HackHype/T2601_APIArduino/T2601_APIArduinoExtentionBoard/M2601_APIArduinoExtentionBoard_Lib3D/CAP-SMD_L4.3-W4.3-H5.3-LS5.1.step

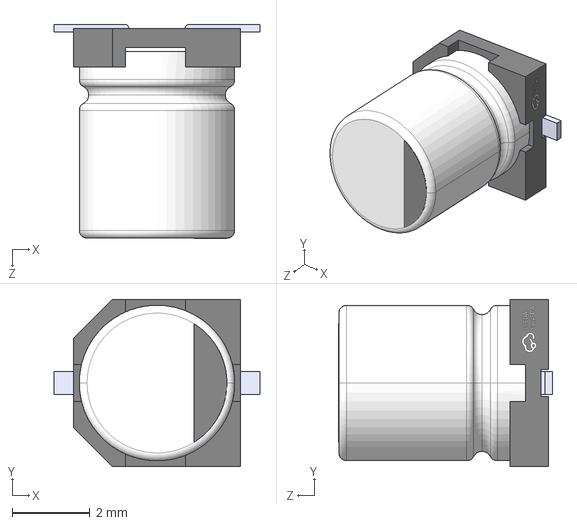
[picture p18: CAD file, 2026-03-15]
T2601_APIArduinoExtentionBoard/M2601_APIArduinoExtentionBoard_Lib3D/CAP-SMD_L4.3-W4.3-H5.3-LS5.1.step
5.30 x 4.30 x 5.51 mm
