HackHype/T2601_APIArduino/T2601_APIArduinoExtentionBoard/M2601_APIArduinoExtentionBoard_Lib3D/USB-C-SMD_HC-TYPE-C-16P-01A.step

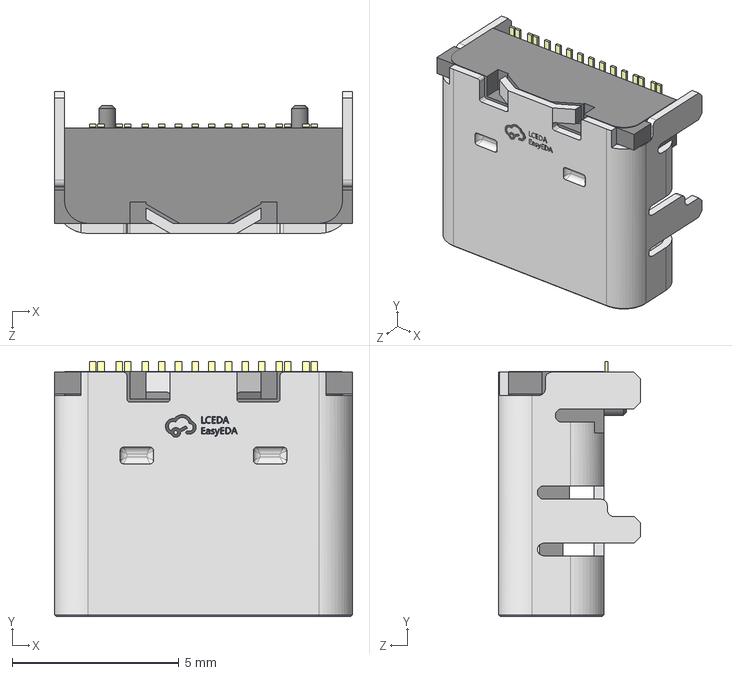
[picture p19: CAD file, 2026-03-15]
T2601_APIArduinoExtentionBoard/M2601_APIArduinoExtentionBoard_Lib3D/USB-C-SMD_HC-TYPE-C-16P-01A.step
8.94 x 7.65 x 4.27 mm
