HackHype/T2601_APIArduino/T2601_APIArduinoExtentionBoard/M2601_APIArduinoExtentionBoard_Lib3D/HTSSOP-16_L5.0-W4.4-P0.65-LS6.4-BL-EP2.5.step

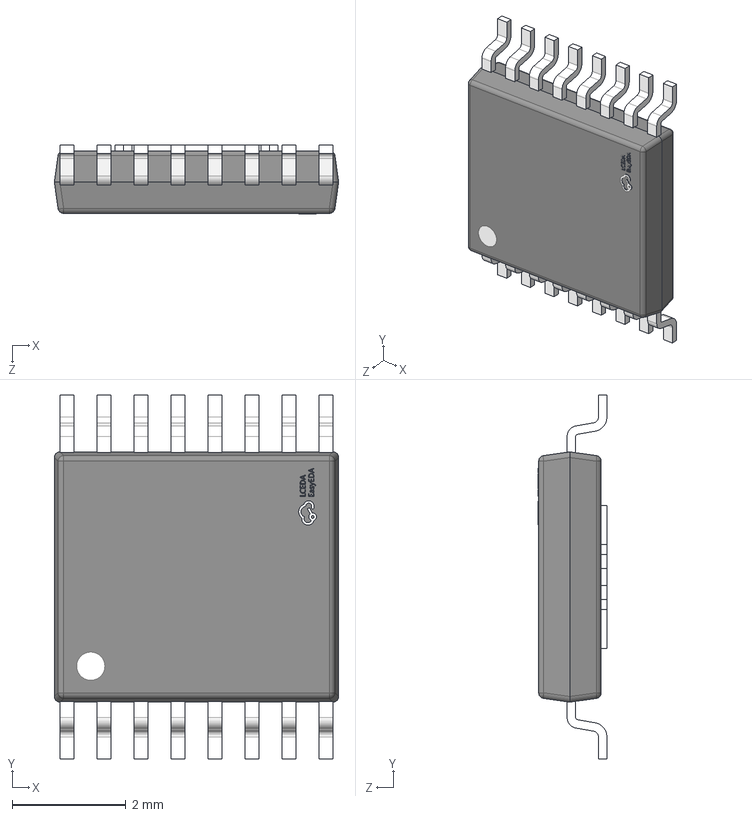
[picture p20: CAD file, 2026-03-15]
T2601_APIArduinoExtentionBoard/M2601_APIArduinoExtentionBoard_Lib3D/HTSSOP-16_L5.0-W4.4-P0.65-LS6.4-BL-EP2.5.step
5.00 x 6.40 x 1.21 mm
