HackHype/T2601_APIArduino/T2601_APIArduinoExtentionBoard/M2601_APIArduinoExtentionBoard_Lib3D/HTSSOP-20_L6.5-W4.4-P0.65-LS6.4-BL-EP3.0.step

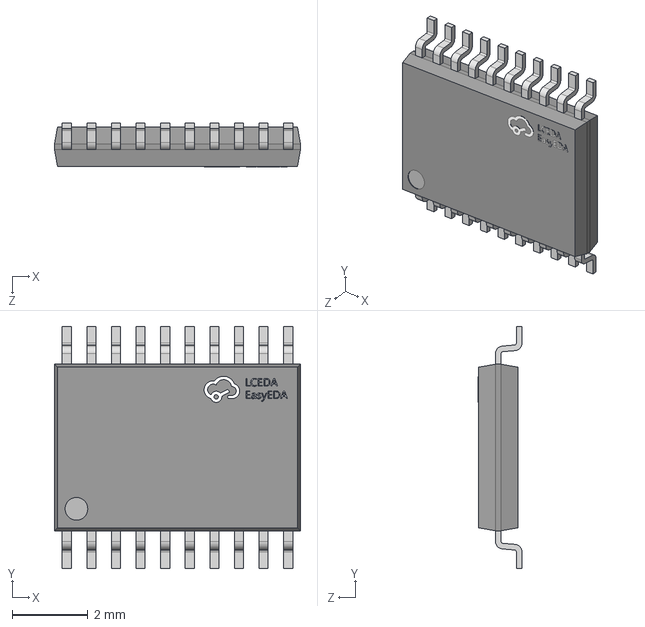
[picture p21: CAD file, 2026-03-15]
T2601_APIArduinoExtentionBoard/M2601_APIArduinoExtentionBoard_Lib3D/HTSSOP-20_L6.5-W4.4-P0.65-LS6.4-BL-EP3.0.step
6.50 x 6.40 x 1.16 mm
