HackHype/T2601_APIArduino/T2601_APIArduinoExtentionBoard/M2601_APIArduinoExtentionBoard_Lib3D/CAP-SMD_BD6.3-L6.6-W6.6-H7.7.step

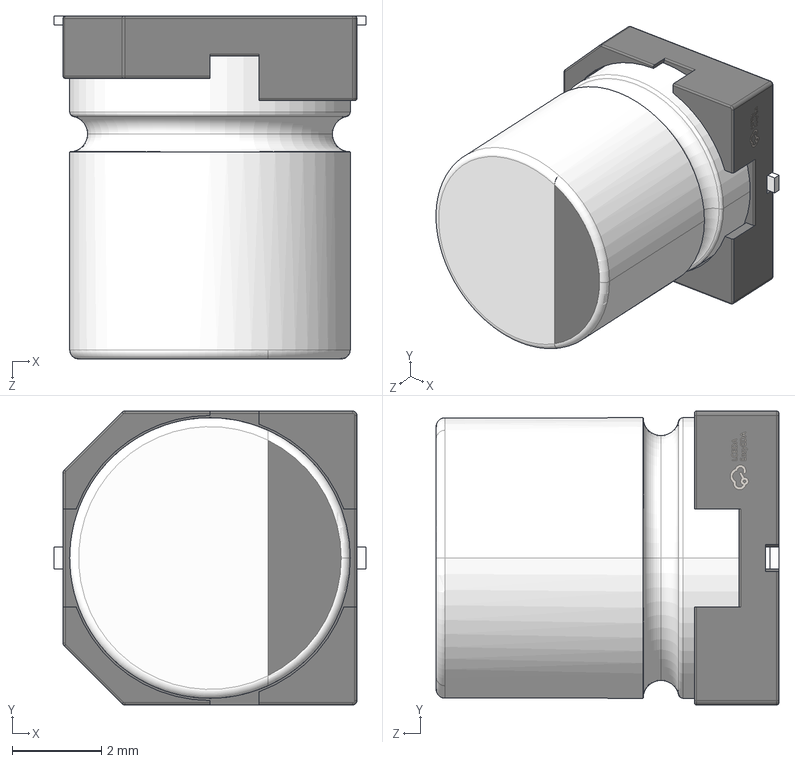
[picture p22: CAD file, 2026-03-15]
T2601_APIArduinoExtentionBoard/M2601_APIArduinoExtentionBoard_Lib3D/CAP-SMD_BD6.3-L6.6-W6.6-H7.7.step
7.00 x 6.60 x 7.70 mm
