HackHype/T2601_APIArduino/T2601_APIArduinoExtentionBoard/M2601_APIArduinoExtentionBoard_Lib3D/QFN-16_L3.0-W3.0-H0.9-P0.50.step

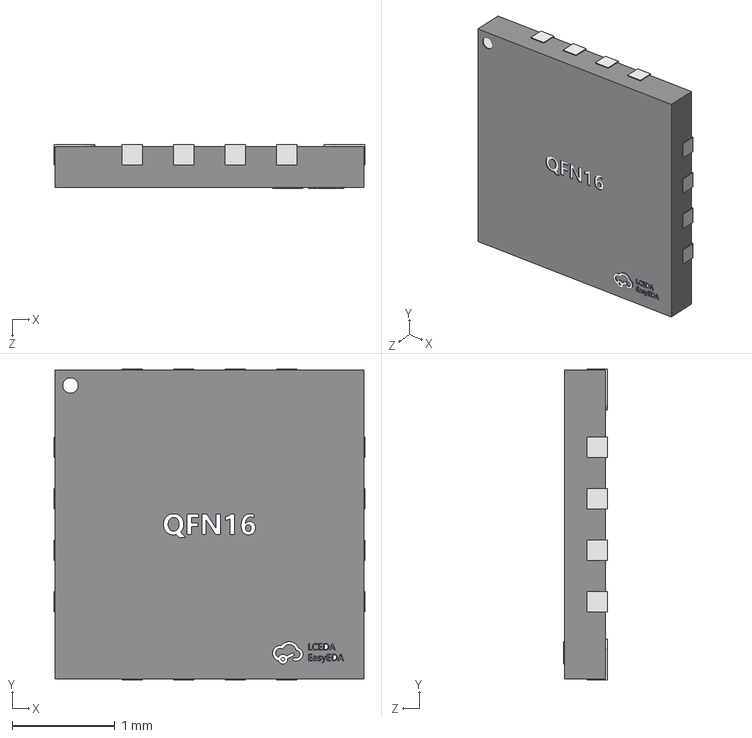
[picture p23: CAD file, 2026-03-15]
T2601_APIArduinoExtentionBoard/M2601_APIArduinoExtentionBoard_Lib3D/QFN-16_L3.0-W3.0-H0.9-P0.50.step
3.02 x 3.02 x 0.43 mm
