HackHype/T2601_APIArduino/T2601_APIArduinoExtentionBoard/M2601_APIArduinoExtentionBoard_Lib3D/IND-SMD_L5.0-W5.0-LQH5BPN1R5NT0L.step

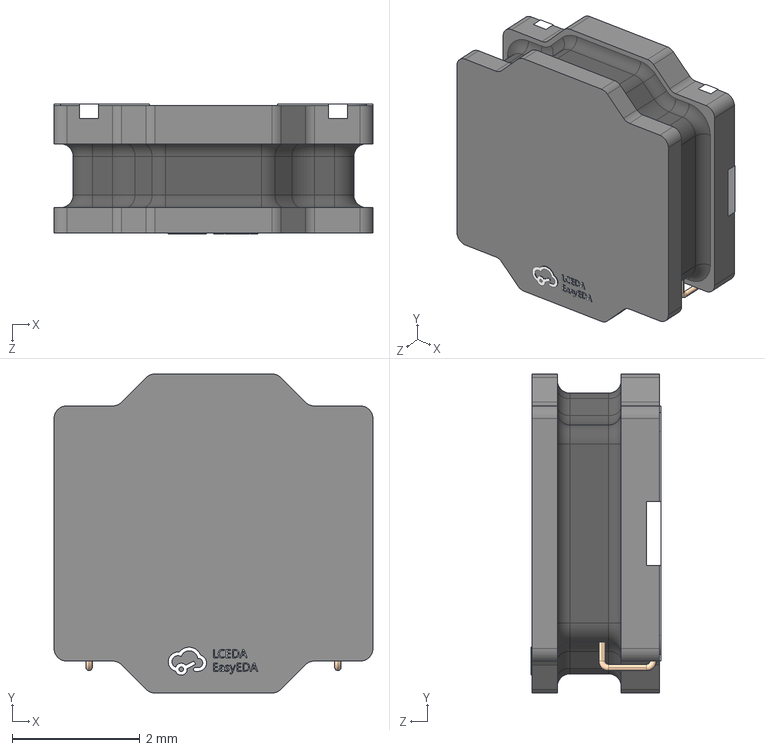
[picture p24: CAD file, 2026-03-15]
T2601_APIArduinoExtentionBoard/M2601_APIArduinoExtentionBoard_Lib3D/IND-SMD_L5.0-W5.0-LQH5BPN1R5NT0L.step
5.00 x 5.00 x 2.03 mm
